jpconstantineau/ErgoTravel/AcrylicCase/Grogdor/pics/2018-05-31 19.27.58.jpg

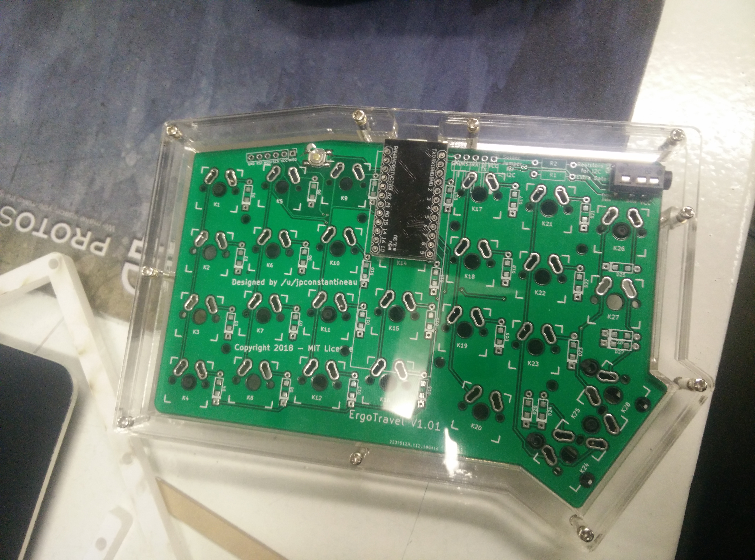
AcrylicCase/Grogdor/pics/2018-05-31 19.27.58.jpg
