jpconstantineau/ErgoTravel/AcrylicCase/Grogdor/pics/2018-05-31 19.28.22.jpg

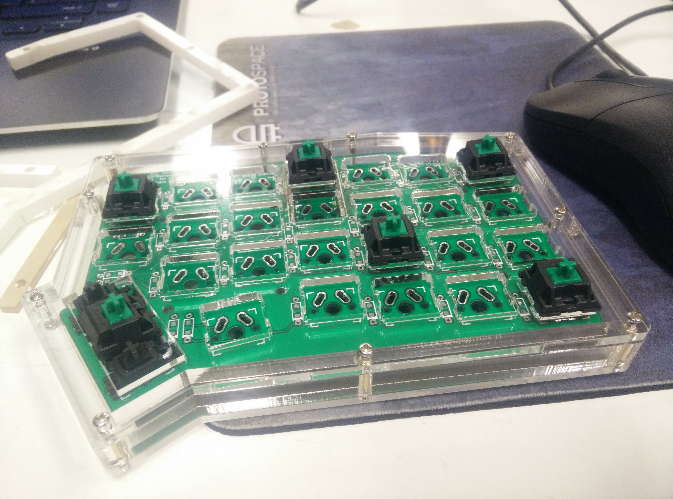
AcrylicCase/Grogdor/pics/2018-05-31 19.28.22.jpg
