jpconstantineau/ErgoTravel/AcrylicCase/Grogdor/pics/2018-05-31 21.10.18.jpg

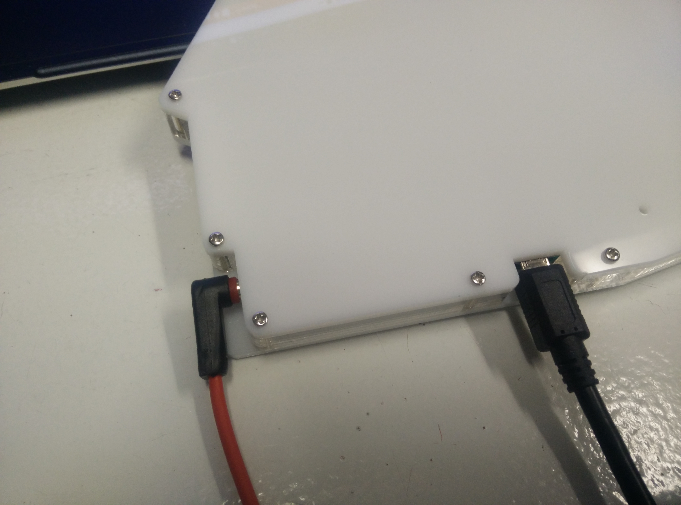
AcrylicCase/Grogdor/pics/2018-05-31 21.10.18.jpg
