jpconstantineau/ErgoTravel/AcrylicCase/Grogdor/pics/2018-05-31 21.10.50.jpg

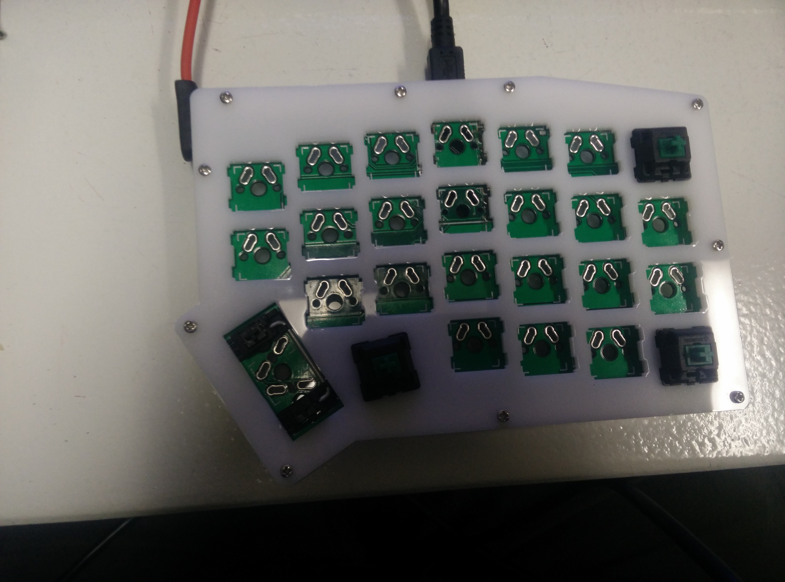
AcrylicCase/Grogdor/pics/2018-05-31 21.10.50.jpg
