jpconstantineau/ErgoTravel/AcrylicCase/Grogdor/pics/2018-05-31 21.47.54.jpg

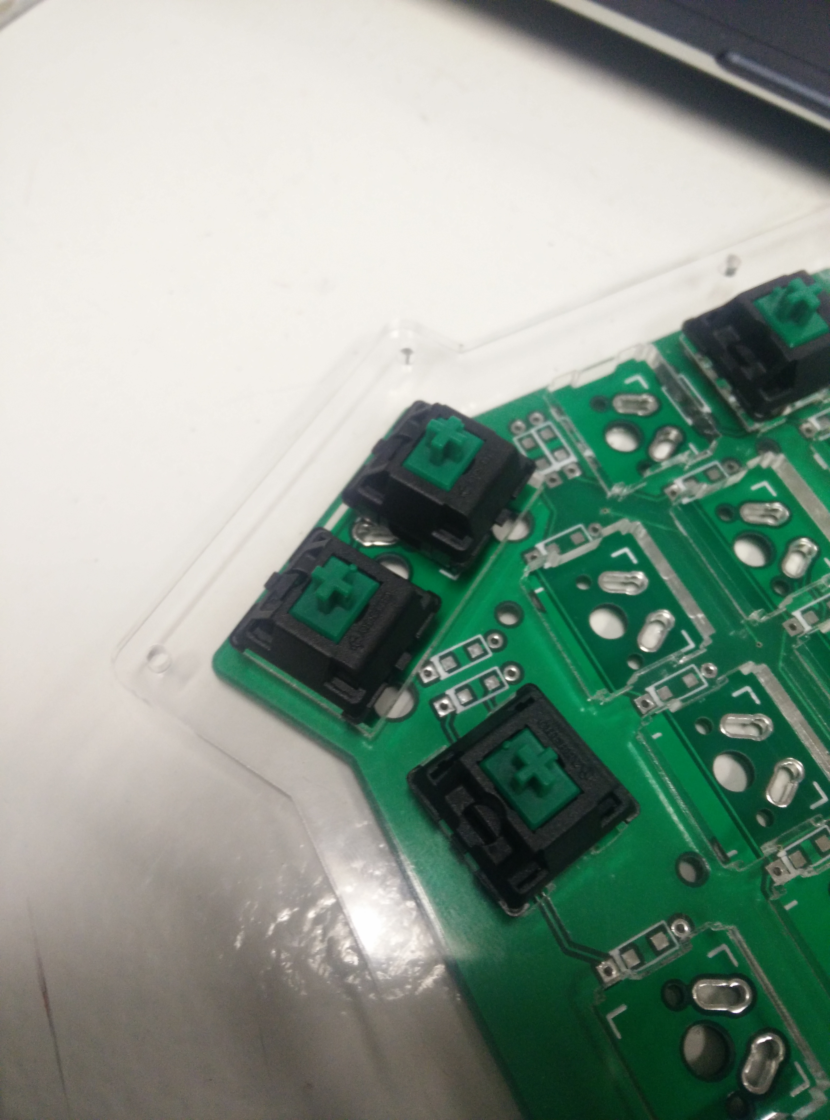
AcrylicCase/Grogdor/pics/2018-05-31 21.47.54.jpg
