jpconstantineau/ErgoTravel/AcrylicCase/Grogdor/pics/2018-05-31 21.59.58.jpg

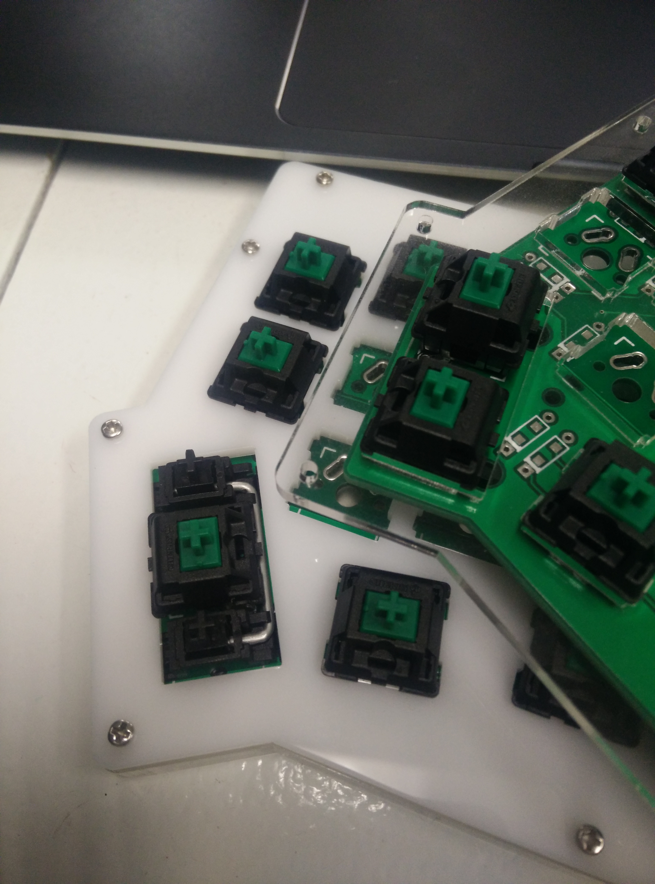
AcrylicCase/Grogdor/pics/2018-05-31 21.59.58.jpg
