jpconstantineau/ErgoTravel/AcrylicCase/Grogdor/pics/2018-05-31 22.29.56.jpg

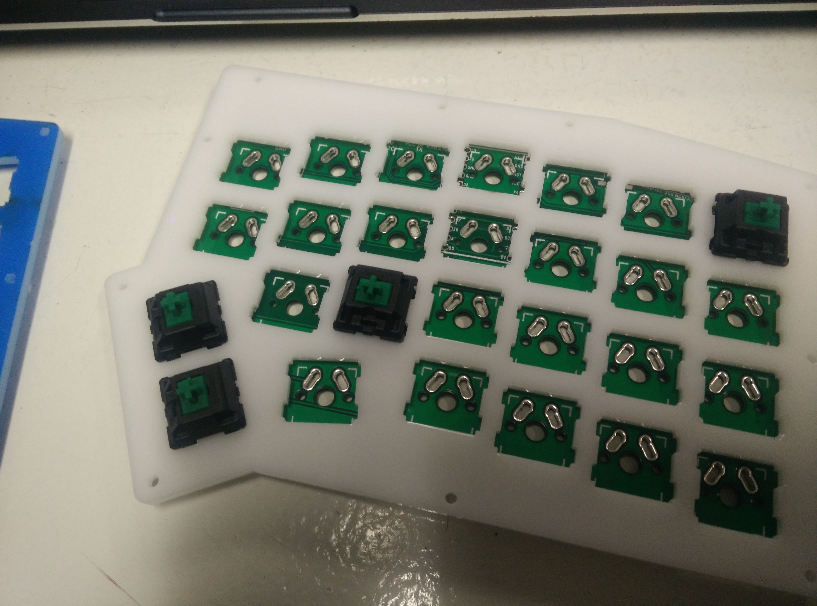
AcrylicCase/Grogdor/pics/2018-05-31 22.29.56.jpg
