jpconstantineau/ErgoTravel/AcrylicCase/Grogdor/pics/2018-06-26 22.19.27c.jpg

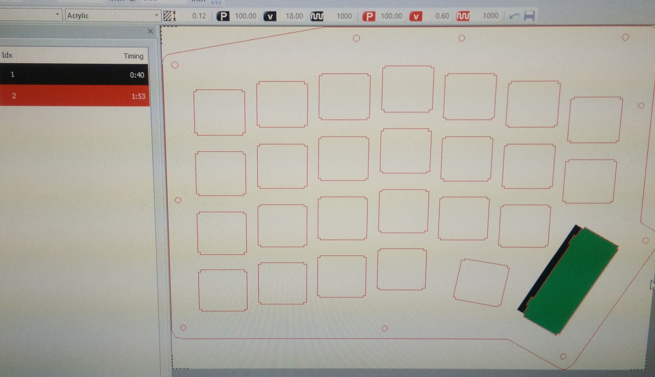
AcrylicCase/Grogdor/pics/2018-06-26 22.19.27c.jpg
