jpconstantineau/ErgoTravel/AcrylicCase/Grogdor/pics/2018-06-26 22.31.41.jpg

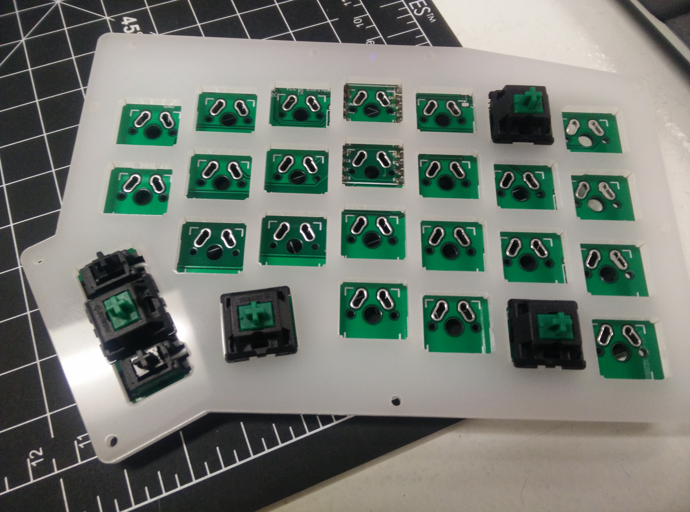
AcrylicCase/Grogdor/pics/2018-06-26 22.31.41.jpg
