jpconstantineau/ErgoTravel/AcrylicCase/Grogdor/pics/2018-06-26 22.33.23.jpg

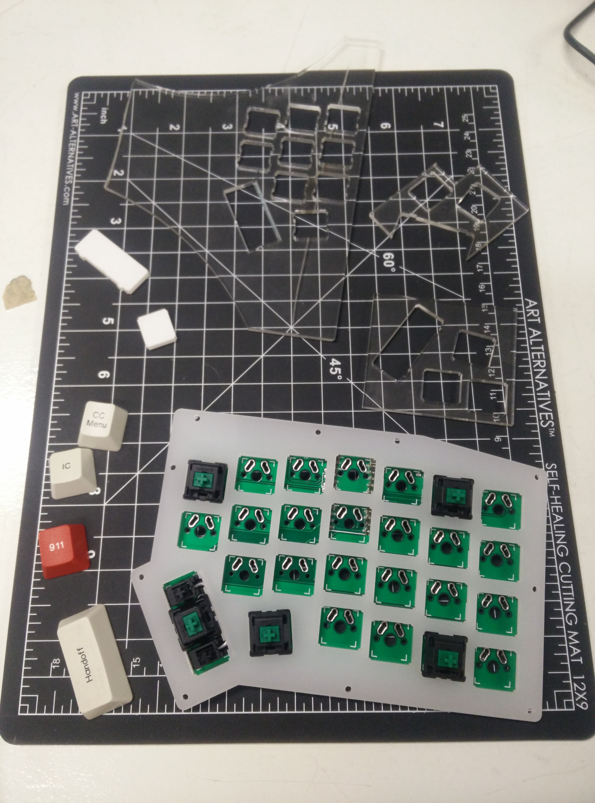
AcrylicCase/Grogdor/pics/2018-06-26 22.33.23.jpg
