jpconstantineau/ErgoTravel/AcrylicCase/Grogdor/pics/2018-06-26 22.34.32.jpg

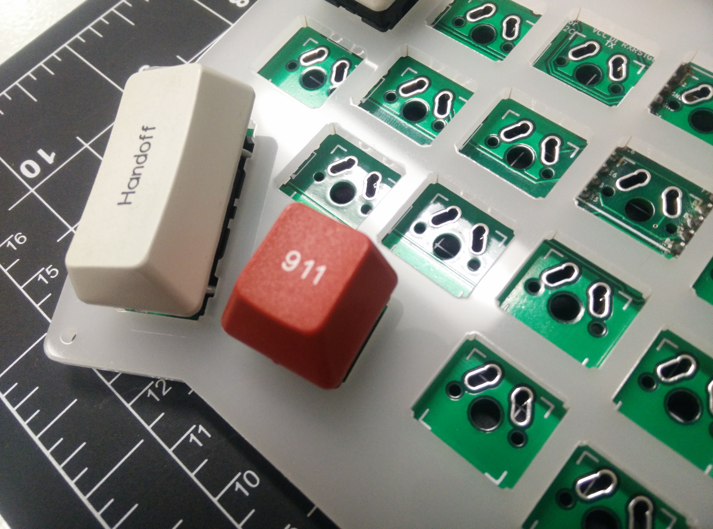
AcrylicCase/Grogdor/pics/2018-06-26 22.34.32.jpg
