jpconstantineau/ErgoTravel/AcrylicCase/Grogdor/pics/2018-06-26 22.34.40c.jpg

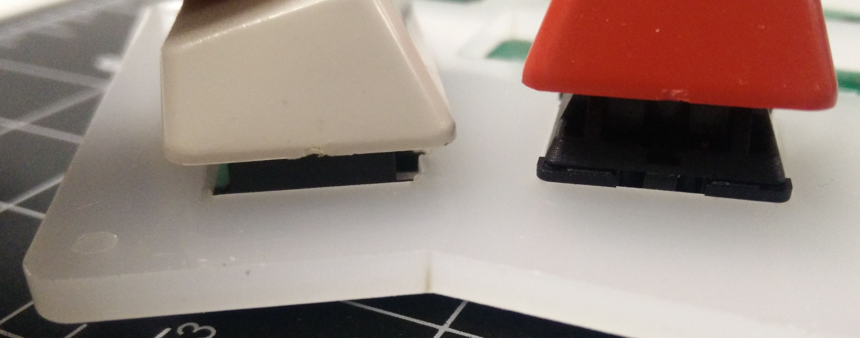
AcrylicCase/Grogdor/pics/2018-06-26 22.34.40c.jpg
