jpconstantineau/ErgoTravel/AcrylicCase/Grogdor/pics/2018-06-26 22.37.25.jpg

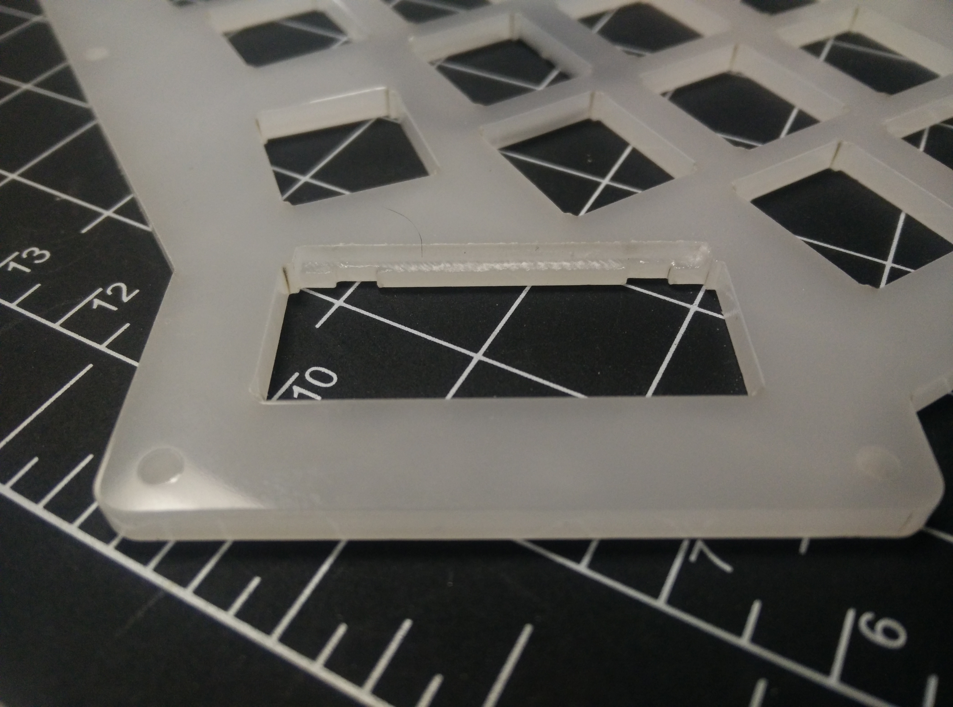
AcrylicCase/Grogdor/pics/2018-06-26 22.37.25.jpg
