jpconstantineau/ErgoTravel/ExternalPCBCase/BottomPlate/Bottom Plate.png

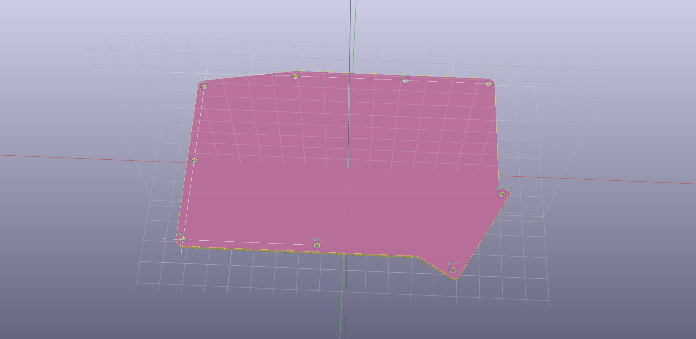
ExternalPCBCase/BottomPlate/Bottom Plate.png
