jpconstantineau/ErgoTravel/ExternalPCBCase/TopPlate1U/Top Plate.png

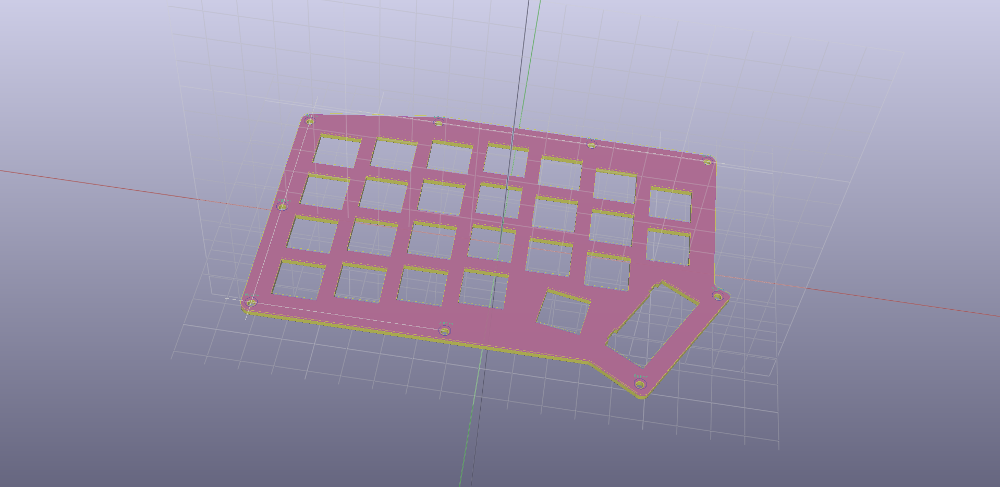
ExternalPCBCase/TopPlate1U/Top Plate.png
