jpconstantineau/ErgoTravel/images/Case_PCB.PNG

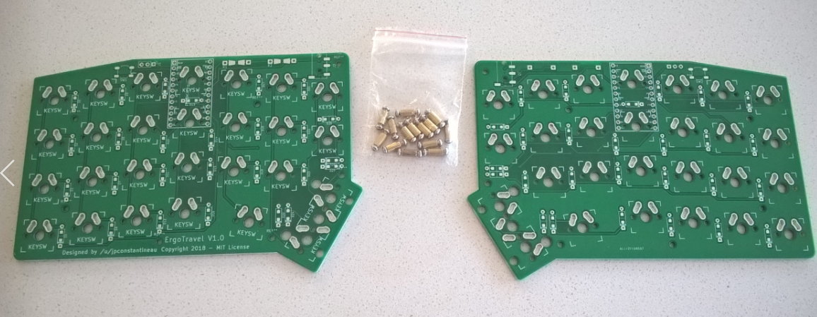
images/Case_PCB.PNG
