jpconstantineau/ErgoTravel/images/Case_Sandwich.PNG

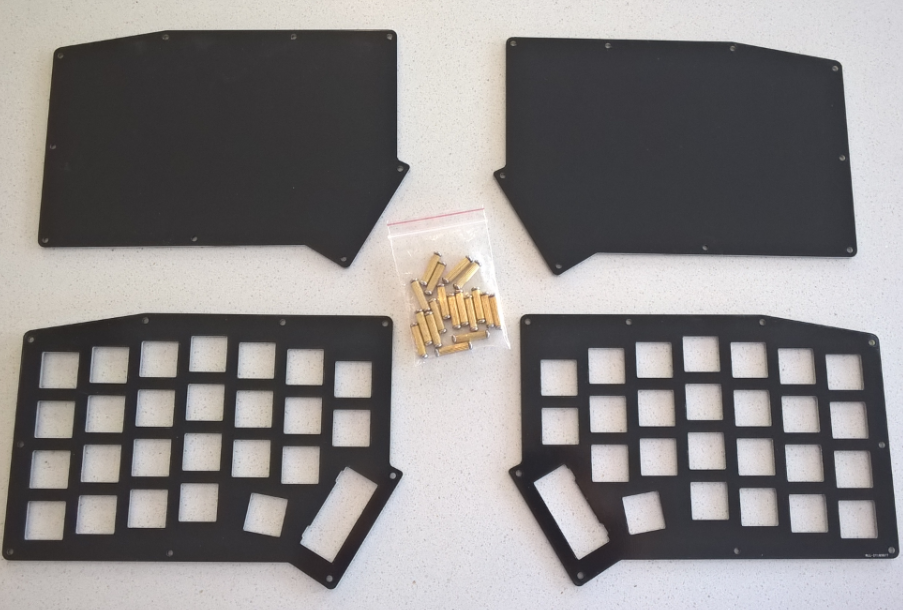
images/Case_Sandwich.PNG
