jpconstantineau/ErgoTravel/images/diodes_back.png

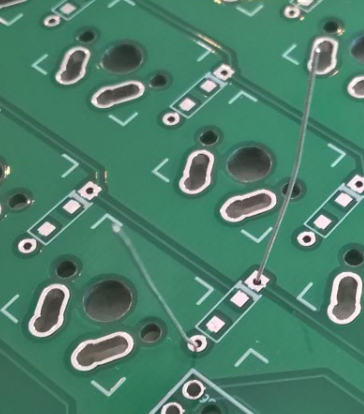
images/diodes_back.png
