jpconstantineau/ErgoTravel/images/first_alps_ergotravel_top.jpg

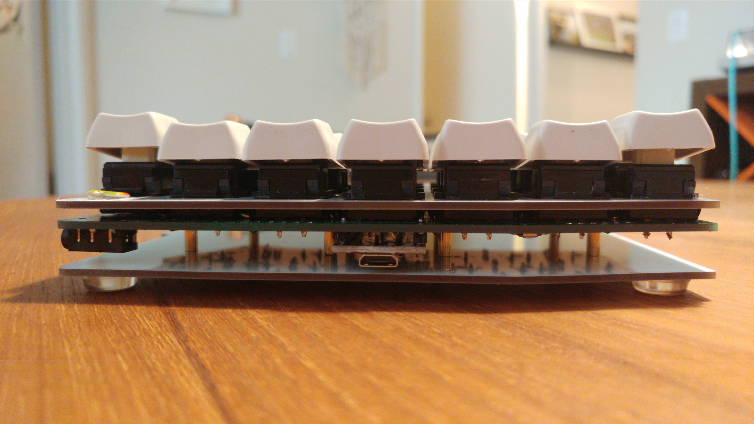
images/first_alps_ergotravel_top.jpg
