jpconstantineau/ErgoTravel/images/Full_Kit.PNG

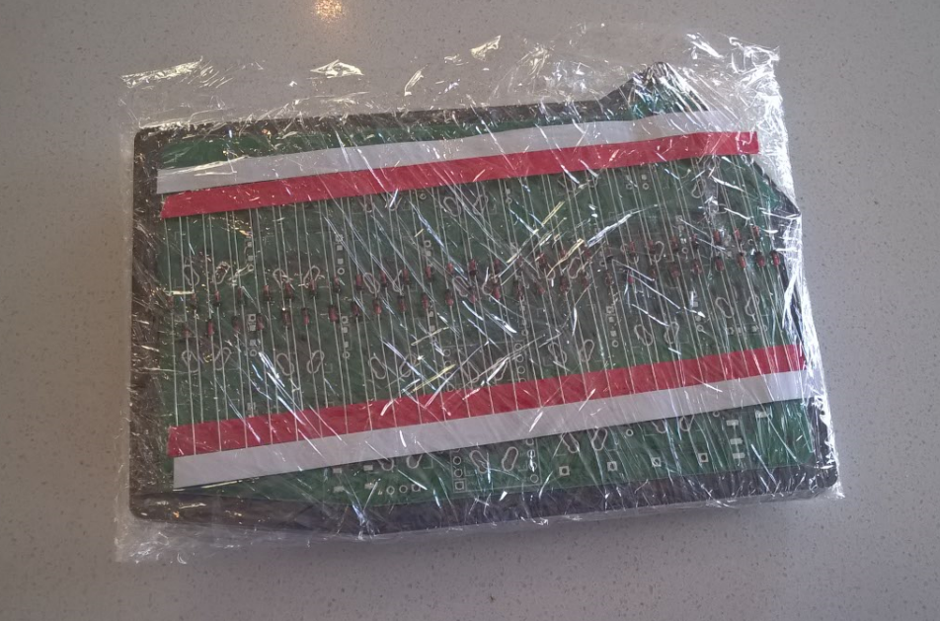
images/Full_Kit.PNG
