jpconstantineau/ErgoTravel/images/Key_Matrix.PNG

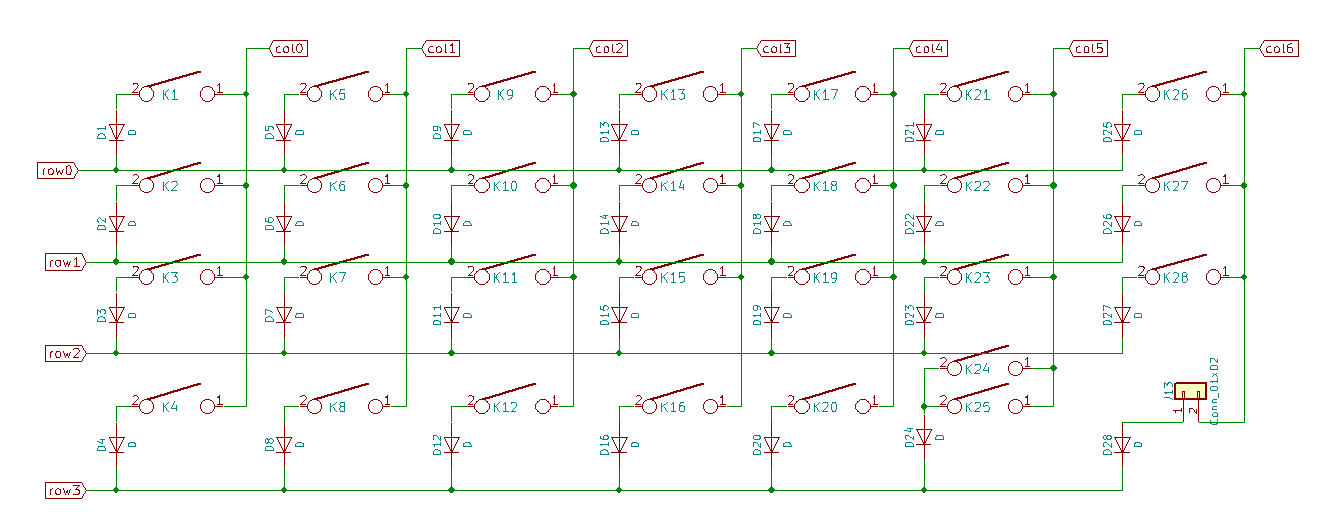
images/Key_Matrix.PNG
