jpconstantineau/ErgoTravel/images/keyboard-layout.2x1U_1x2U.png

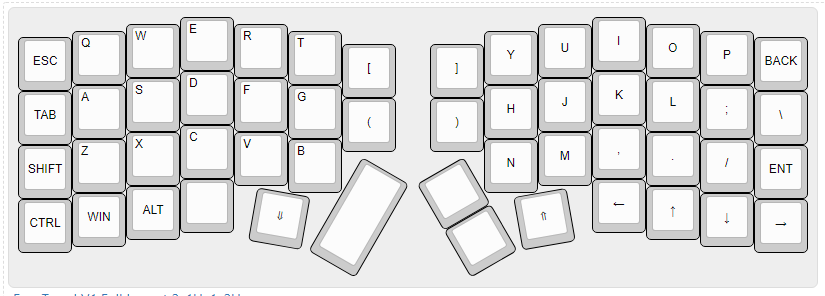
images/keyboard-layout.2x1U_1x2U.png
