jpconstantineau/ErgoTravel/images/PCB_V1.0_Left.PNG

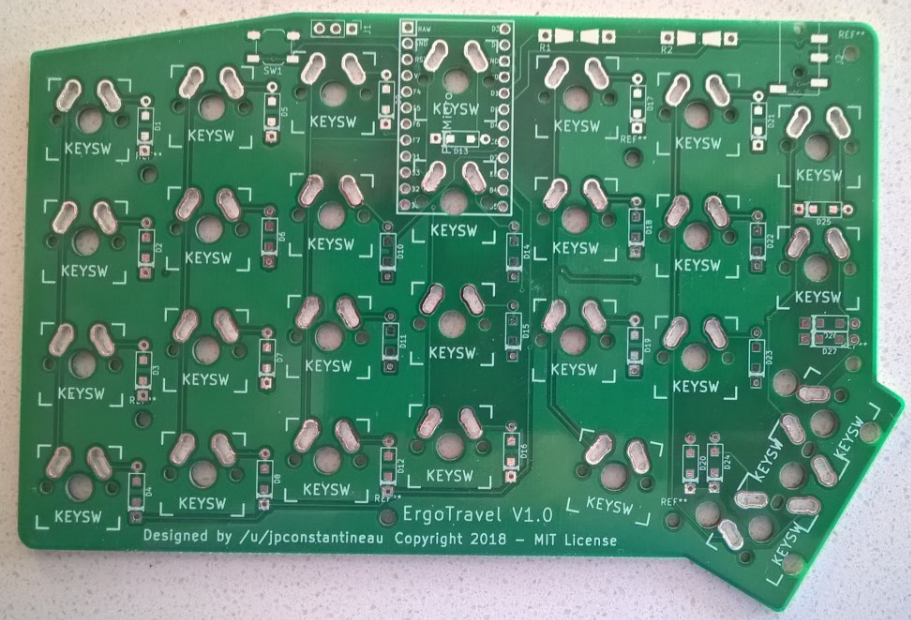
images/PCB_V1.0_Left.PNG
