jpconstantineau/ErgoTravel/images/PCB_V1.0_Right.PNG

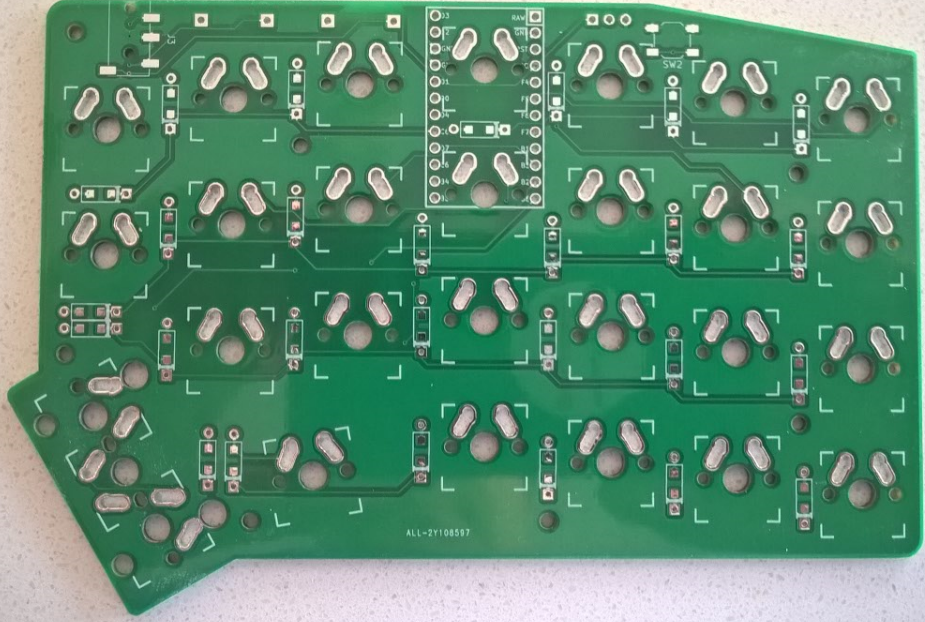
images/PCB_V1.0_Right.PNG
