jpconstantineau/ErgoTravel/images/RGB_strip_connections.jpg

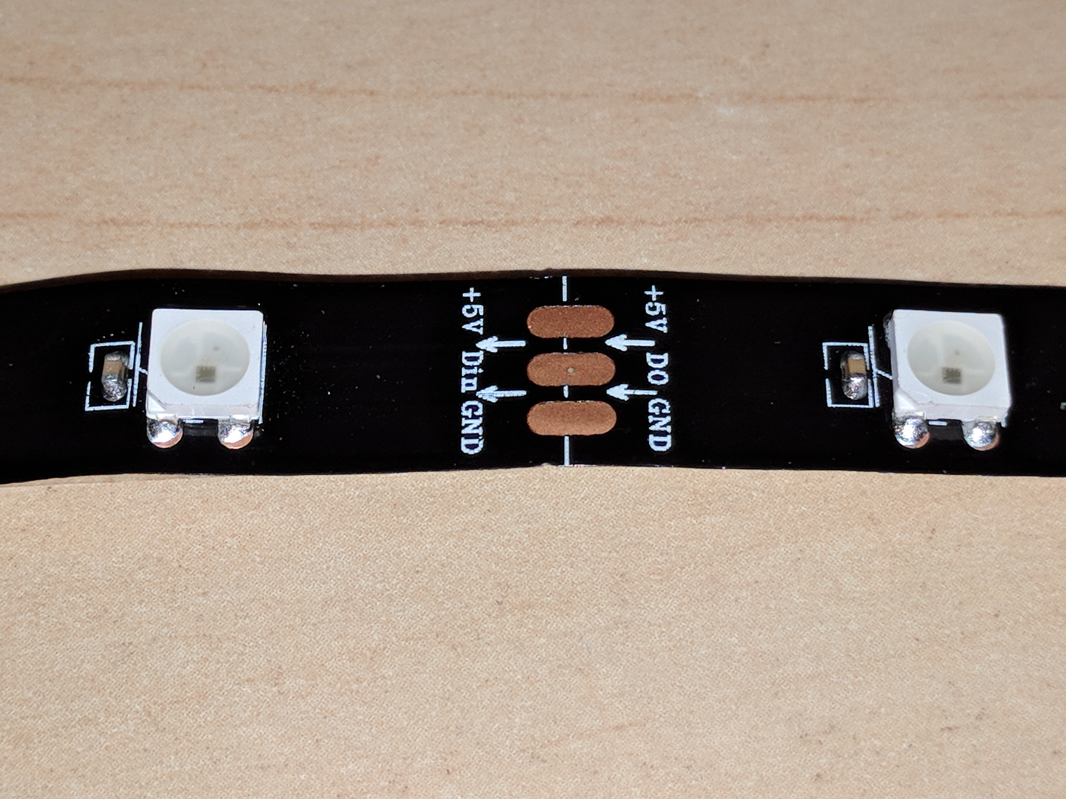
images/RGB_strip_connections.jpg
