jpconstantineau/ErgoTravel/images/stabilizerlegs_1.png

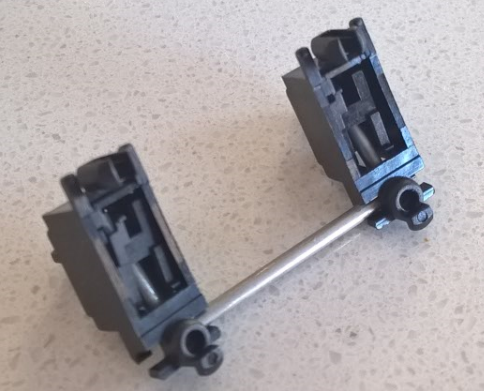
images/stabilizerlegs_1.png
