jpconstantineau/ErgoTravel/PCB/ErgoTravelPCBV1.PNG

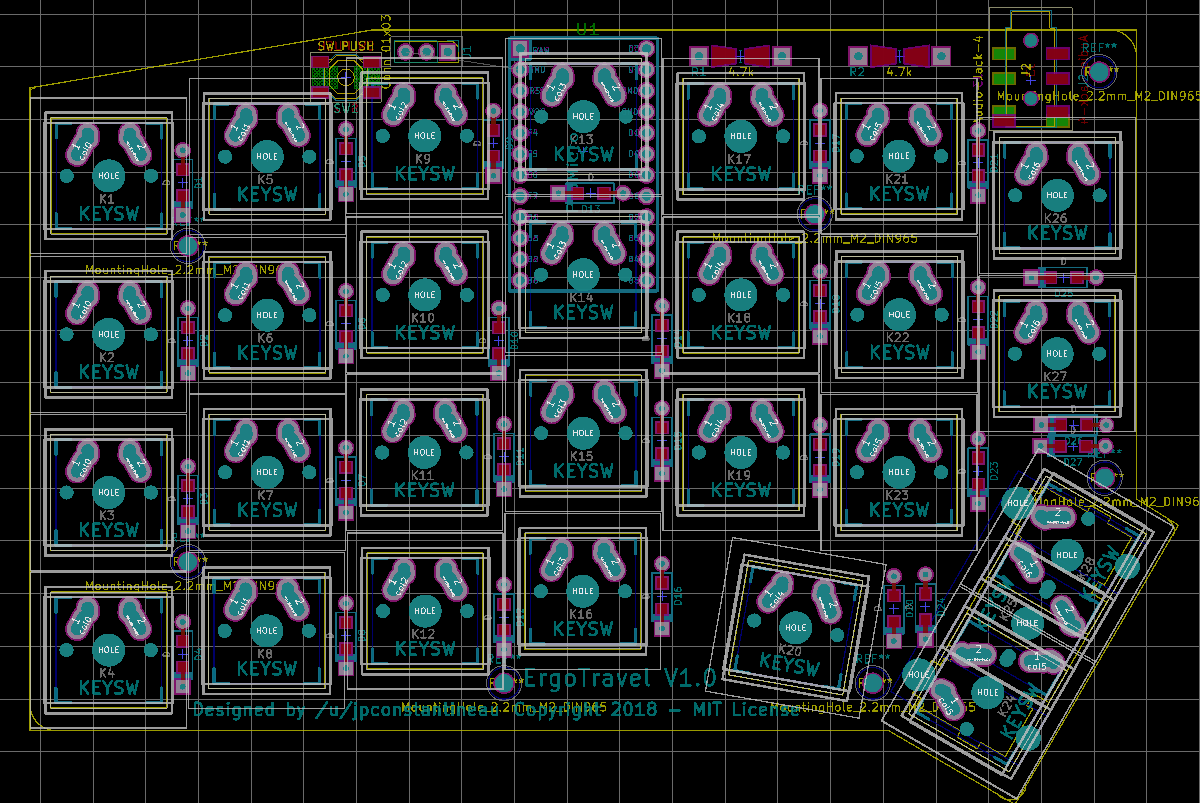
PCB/ErgoTravelPCBV1.PNG
