jpconstantineau/ErgoTravel/Reference/Kailh-.png

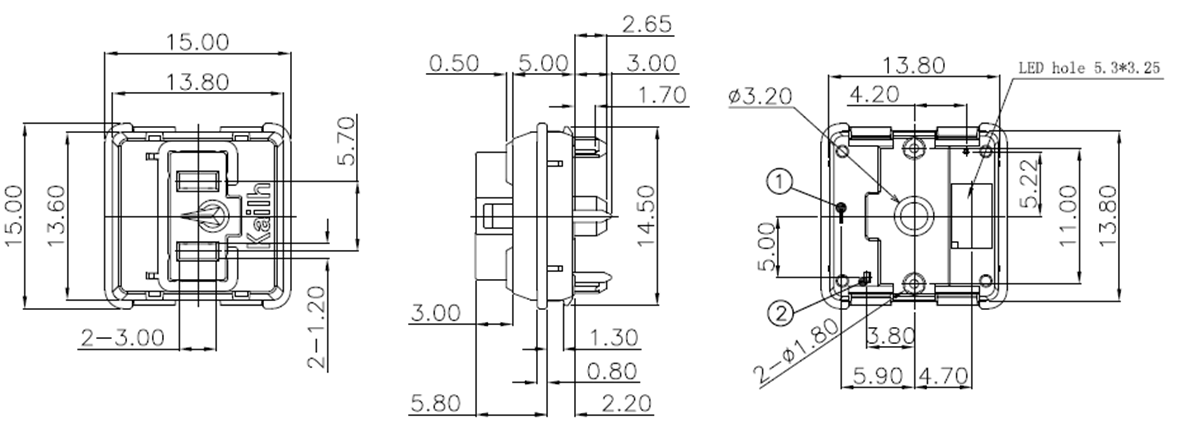
Reference/Kailh-.png
