jpconstantineau/ErgoTravel/AcrylicCase/Grogdor/everything DFM8.dxf

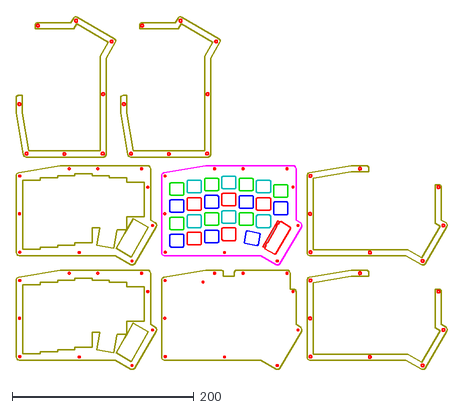
[picture p61: CAD file, 2019-04-07]
AcrylicCase/Grogdor/everything DFM8.dxf
474.9 x 388.8
