jpconstantineau/ErgoTravel/AcrylicCase/jpconstantineau/3dMids/3dmids_prototype_3.stl

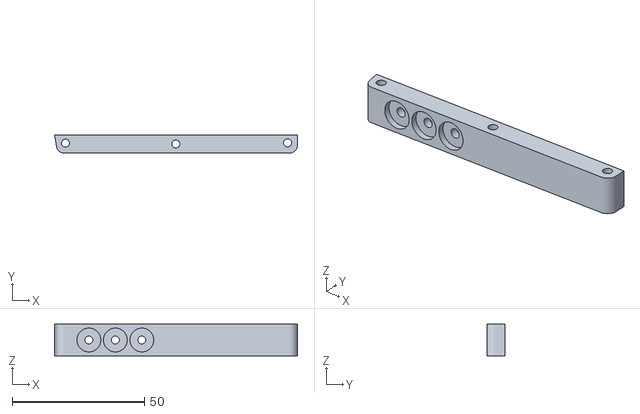
[picture p62: CAD file, 2019-11-17]
AcrylicCase/jpconstantineau/3dMids/3dmids_prototype_3.stl
91.8 x 6.89 x 12.0
