jpconstantineau/ErgoTravel/ExternalPCBCase/BottomPlate/Bottom Plate-F.Cu.dxf

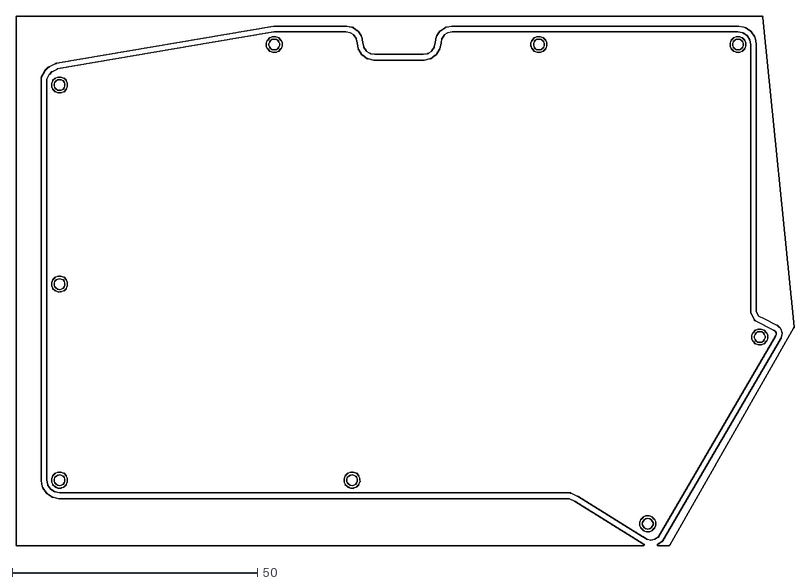
[picture p63: CAD file, 2018-06-02]
ExternalPCBCase/BottomPlate/Bottom Plate-F.Cu.dxf
158.7 x 108.0
