jpconstantineau/ErgoTravel/ExternalPCBCase/TopPlateCombined/Top Plate-brd.dxf

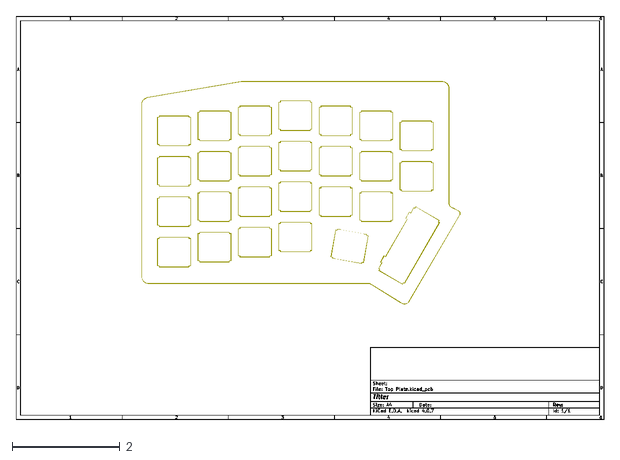
[picture p64: CAD file, 2018-06-02]
ExternalPCBCase/TopPlateCombined/Top Plate-brd.dxf
10.9 x 7.49
