jpconstantineau/ErgoTravel/InternalPCBCase/TopPlate2U/TravelDox-Eco2.User.dxf

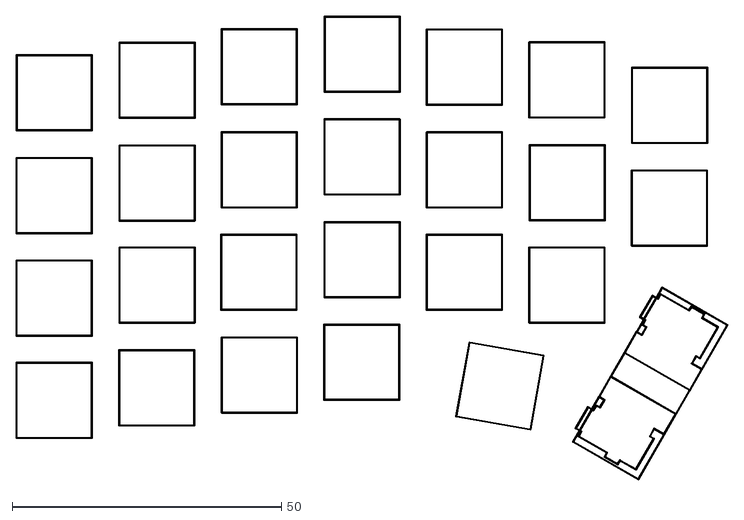
[picture p65: CAD file, 2018-03-09]
InternalPCBCase/TopPlate2U/TravelDox-Eco2.User.dxf
132.2 x 86.1
