jpconstantineau/ErgoTravel/Layout/ErgoTravel_2U_MX.dxf

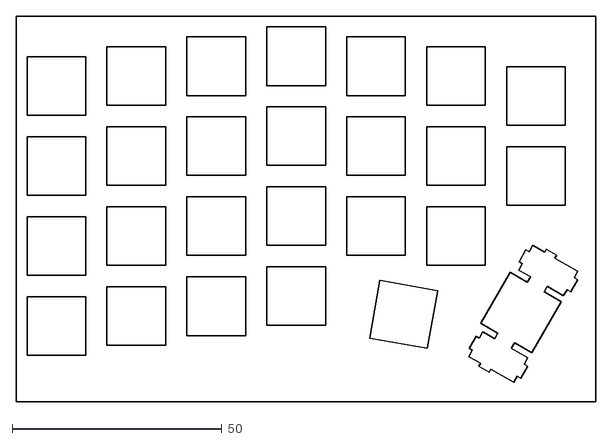
[picture p66: CAD file, 2018-03-09]
Layout/ErgoTravel_2U_MX.dxf
138.0 x 91.9
