jpconstantineau/ErgoTravel/3DPrintedCase/jpconstantineau/MxApls10degree.dxf

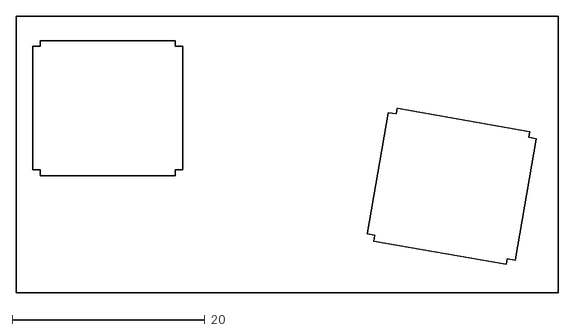
[picture p67: CAD file, 2018-05-28]
3DPrintedCase/jpconstantineau/MxApls10degree.dxf
56.3 x 28.7
