jpconstantineau/ErgoTravel/3DPrintedCase/lbibass/low_profile_right.stl

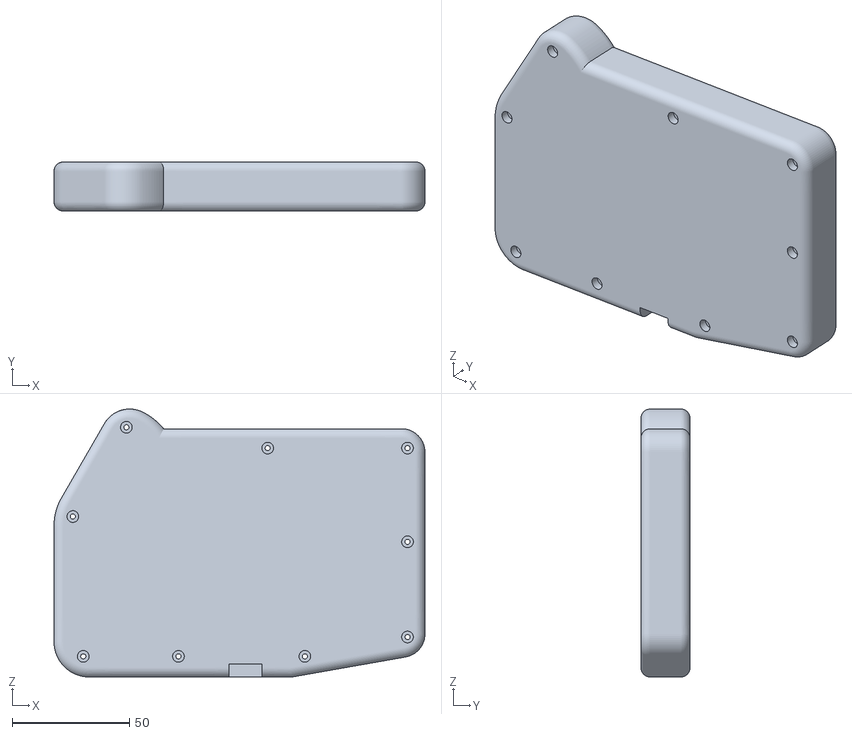
[picture p68: CAD file, 2018-05-11]
3DPrintedCase/lbibass/low_profile_right.stl
158.4 x 21.0 x 114.4
