jpconstantineau/ErgoTravel/AcrylicCase/Grogdor/hipro only bluemicro DFM9.dxf

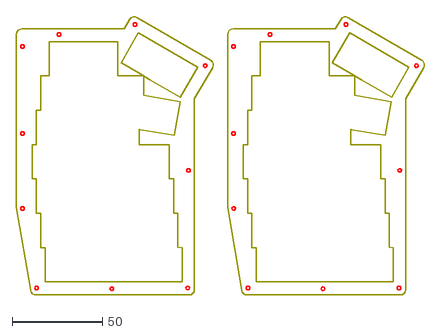
[picture p69: CAD file, 2019-04-07]
AcrylicCase/Grogdor/hipro only bluemicro DFM9.dxf
226.7 x 154.9
