jpconstantineau/ErgoTravel/ExternalPCBCase/BottomPlate/Bottom Plate-B.Cu.dxf

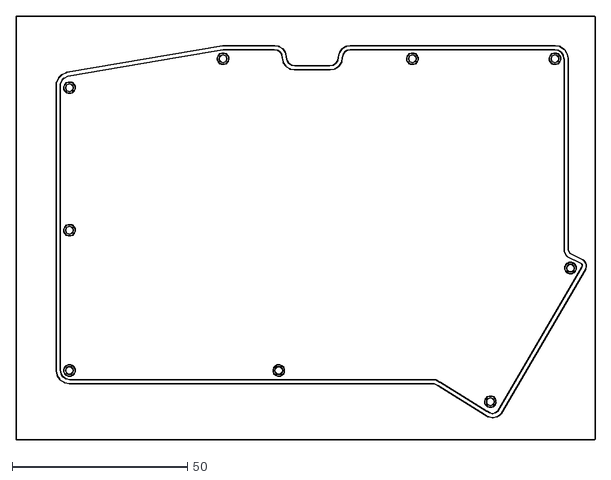
[picture p70: CAD file, 2018-06-02]
ExternalPCBCase/BottomPlate/Bottom Plate-B.Cu.dxf
165.1 x 120.7
