jpconstantineau/ErgoTravel/ExternalPCBCase/TopPlate1U/Top Plate-Edge.Cuts.dxf

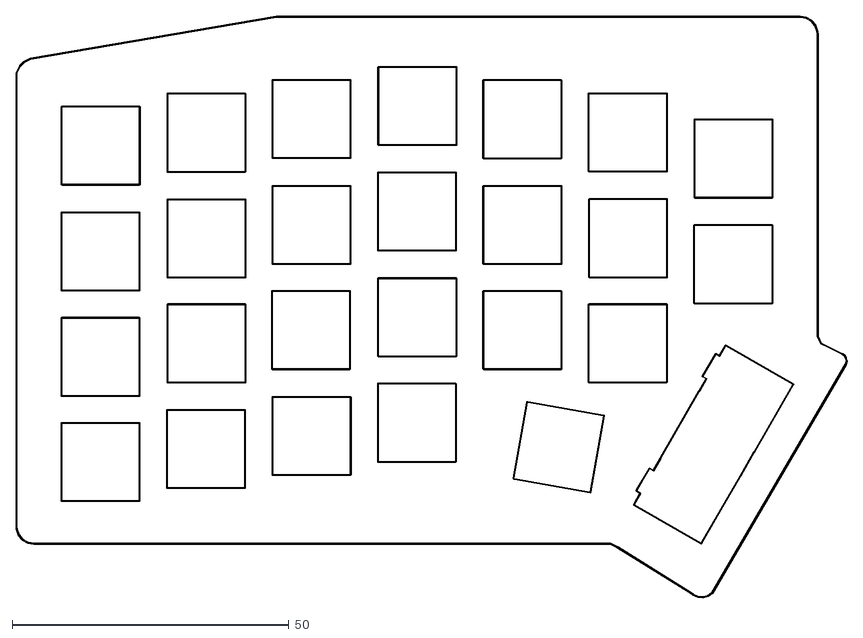
[picture p71: CAD file, 2018-04-29]
ExternalPCBCase/TopPlate1U/Top Plate-Edge.Cuts.dxf
150.2 x 105.1
