jpconstantineau/ErgoTravel/ExternalPCBCase/TopPlateCombined/Top Plate-Edge.Cuts.dxf

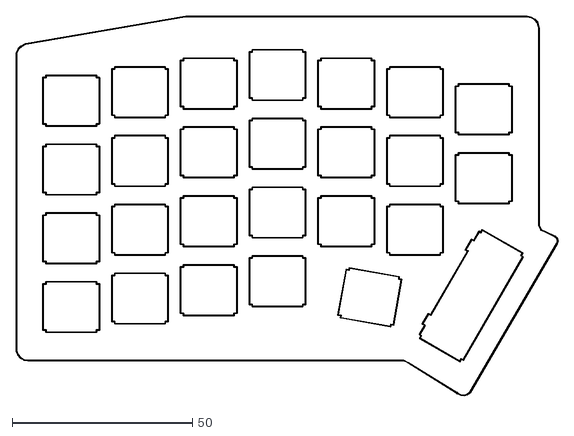
[picture p72: CAD file, 2018-06-02]
ExternalPCBCase/TopPlateCombined/Top Plate-Edge.Cuts.dxf
150.2 x 105.1
