jpconstantineau/ErgoTravel/Layout/ErgoTravel_1u.dxf

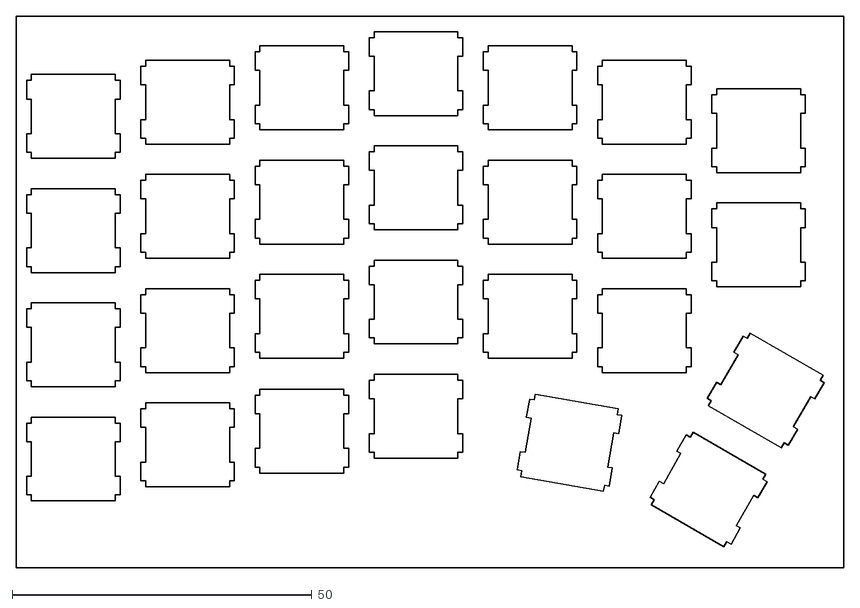
[picture p73: CAD file, 2018-03-09]
Layout/ErgoTravel_1u.dxf
138.0 x 91.9
