jpconstantineau/ErgoTravel/3DPrintedCase/jpconstantineau/MXAlps.dxf

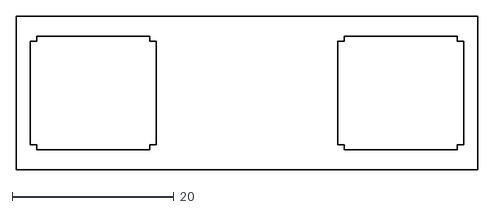
[picture p74: CAD file, 2018-05-28]
3DPrintedCase/jpconstantineau/MXAlps.dxf
57.2 x 19.0
