jpconstantineau/ErgoTravel/AcrylicCase/Grogdor/top only bluemicro DFM9.dxf

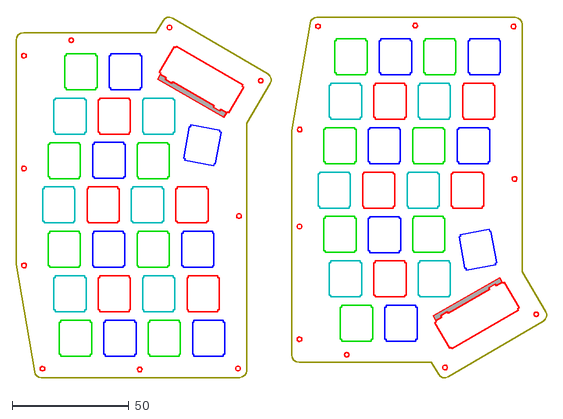
[picture p75: CAD file, 2019-04-07]
AcrylicCase/Grogdor/top only bluemicro DFM9.dxf
227.6 x 155.4
