jpconstantineau/ErgoTravel/AcrylicCase/jpconstantineau/3dMids/3dmids_prototype.stl

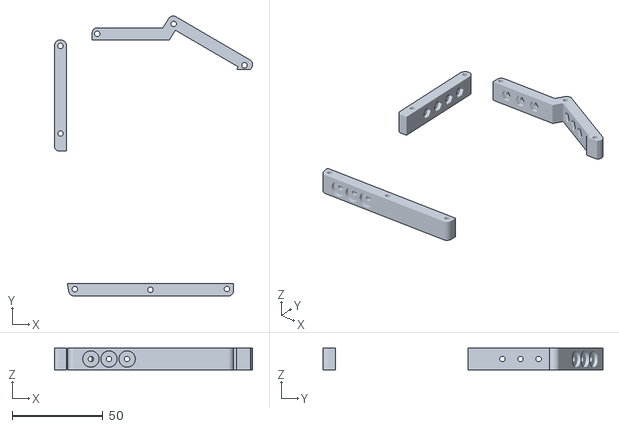
[picture p76: CAD file, 2019-11-17]
AcrylicCase/jpconstantineau/3dMids/3dmids_prototype.stl
109.3 x 154.5 x 12.0
