jpconstantineau/ErgoTravel/Layout/ErgoTravel_1U_MX.dxf

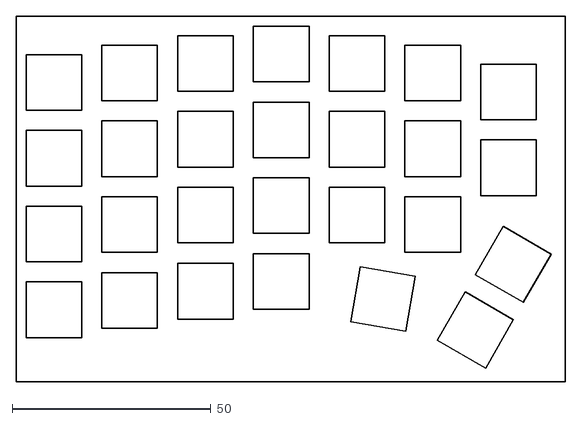
[picture p77: CAD file, 2018-03-09]
Layout/ErgoTravel_1U_MX.dxf
138.0 x 91.9
