jpconstantineau/ErgoTravel/3DPrintedCase/jpconstantineau/mxalps2u30degree.dxf

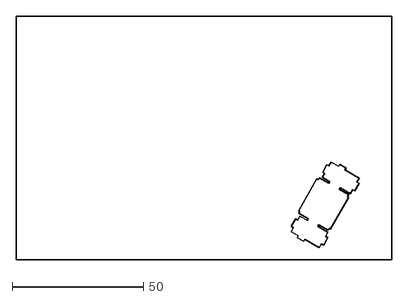
[picture p78: CAD file, 2018-05-28]
3DPrintedCase/jpconstantineau/mxalps2u30degree.dxf
142.9 x 92.8
