jpconstantineau/ErgoTravel/AcrylicCase/Grogdor/bottoms only DFM8.dxf

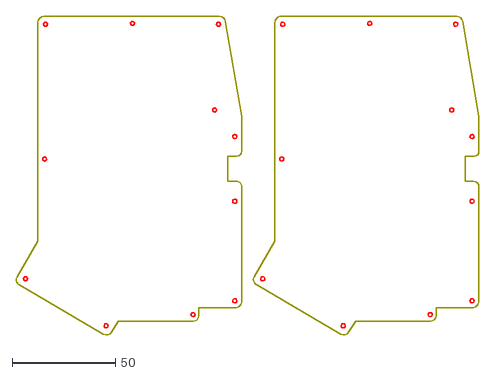
[picture p79: CAD file, 2019-04-07]
AcrylicCase/Grogdor/bottoms only DFM8.dxf
224.4 x 154.9
