jpconstantineau/ErgoTravel/AcrylicCase/jpconstantineau/3dMids/mids only DFM8.dxf

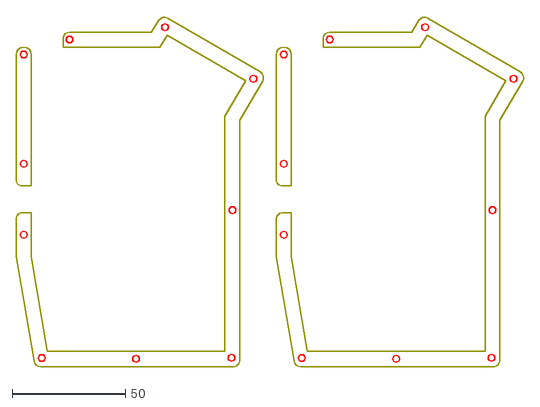
[picture p80: CAD file, 2019-04-07]
AcrylicCase/jpconstantineau/3dMids/mids only DFM8.dxf
224.4 x 154.9
