jpconstantineau/ErgoTravel/3DPrintedCase/jpconstantineau/mxapls30degree.dxf

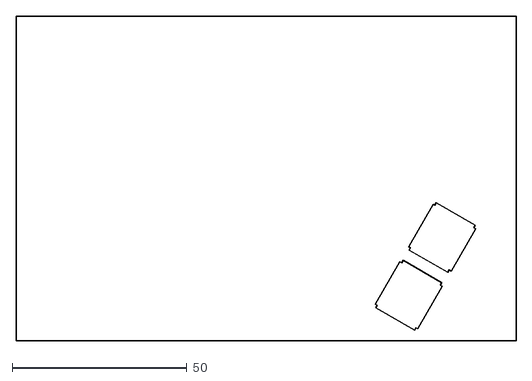
[picture p81: CAD file, 2018-05-28]
3DPrintedCase/jpconstantineau/mxapls30degree.dxf
142.9 x 92.8
