jpconstantineau/ErgoTravel/AcrylicCase/Grogdor/bottoms only bluemicro DFM9.dxf

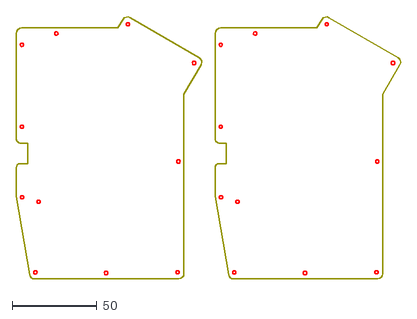
[picture p82: CAD file, 2019-04-07]
AcrylicCase/Grogdor/bottoms only bluemicro DFM9.dxf
226.7 x 154.9
