jpconstantineau/ErgoTravel/3DPrintedCase/jpconstantineau/2UMX.dxf

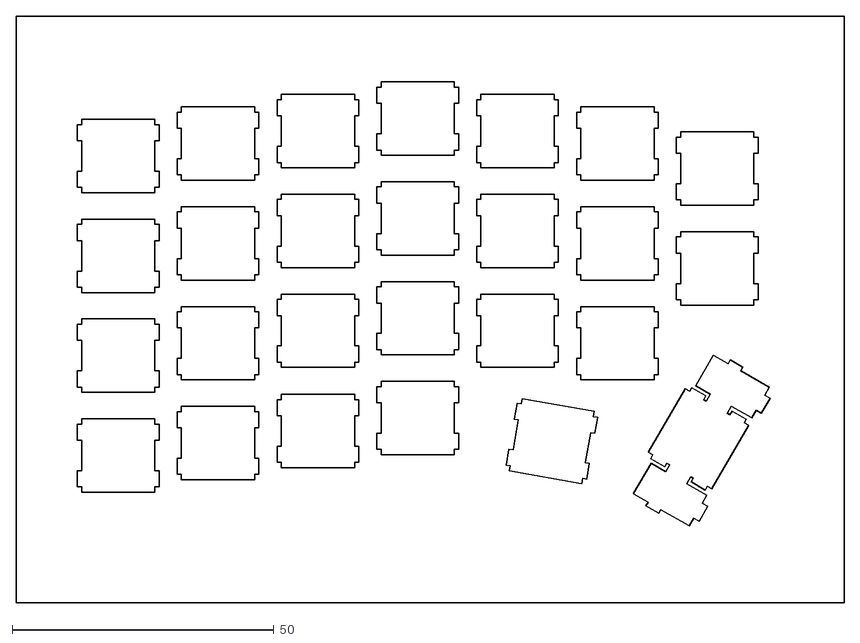
[picture p83: CAD file, 2018-03-27]
3DPrintedCase/jpconstantineau/2UMX.dxf
158.0 x 111.9
