jpconstantineau/ErgoTravel/3DPrintedCase/jpconstantineau/1UMXApls.dxf

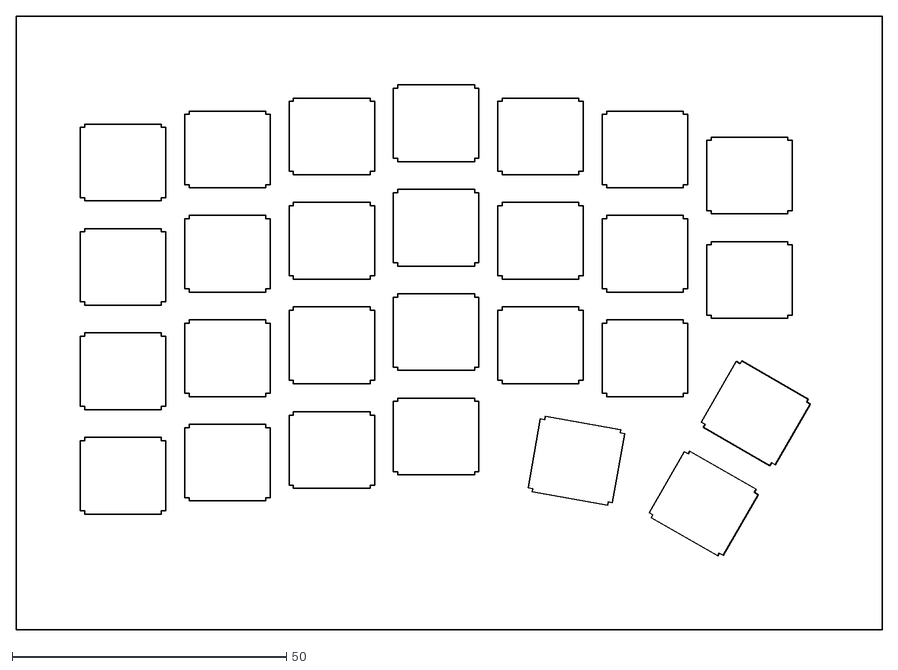
[picture p84: CAD file, 2018-03-27]
3DPrintedCase/jpconstantineau/1UMXApls.dxf
158.0 x 111.9
