jpconstantineau/ErgoTravel/AcrylicCase/Grogdor/midlittles only DFM8.dxf

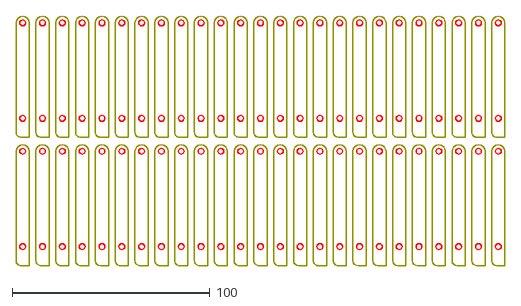
[picture p85: CAD file, 2019-04-07]
AcrylicCase/Grogdor/midlittles only DFM8.dxf
247.5 x 126.3
