jpconstantineau/ErgoTravel/3DPrintedCase/jpconstantineau/1UMX.dxf

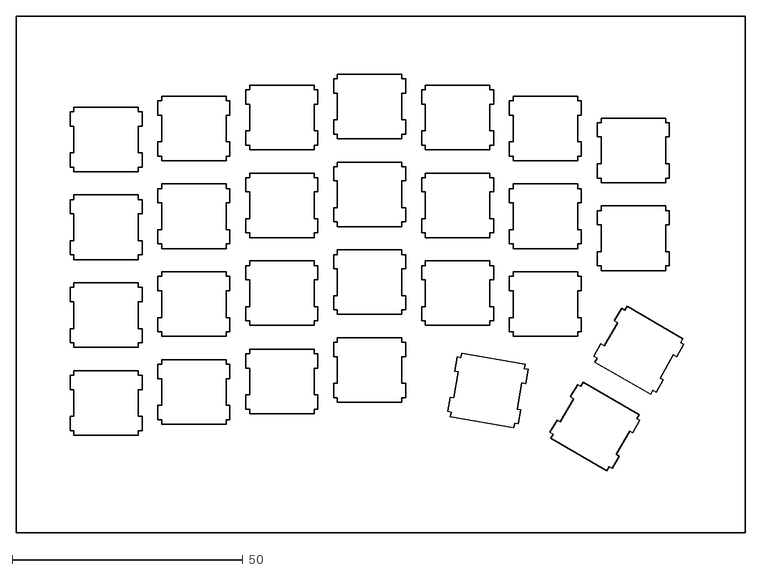
[picture p86: CAD file, 2018-03-27]
3DPrintedCase/jpconstantineau/1UMX.dxf
158.0 x 111.9
