jpconstantineau/ErgoTravel/AcrylicCase/Grogdor/everything nite.dxf

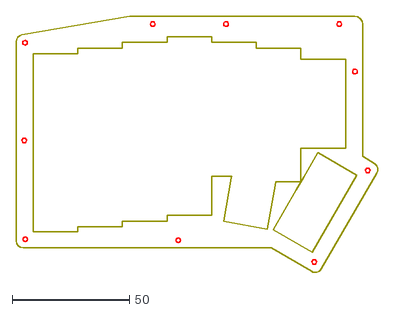
[picture p87: CAD file, 2019-04-07]
AcrylicCase/Grogdor/everything nite.dxf
154.9 x 109.4
