jpconstantineau/ErgoTravel/3DPrintedCase/jpconstantineau/MXAlps2.dxf

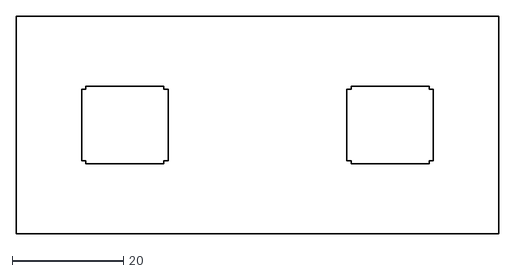
[picture p88: CAD file, 2018-03-27]
3DPrintedCase/jpconstantineau/MXAlps2.dxf
86.7 x 39.1
