jpconstantineau/ErgoTravel/AcrylicCase/Grogdor/everything DFM9.dxf

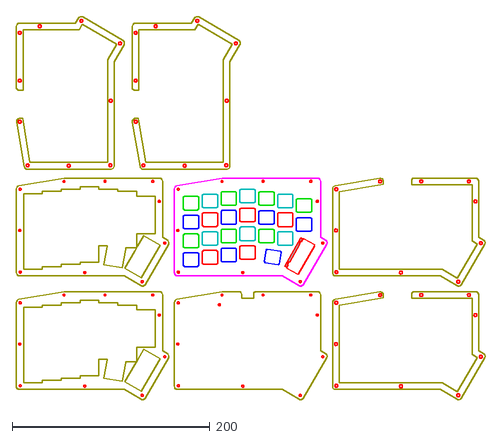
[picture p89: CAD file, 2019-04-07]
AcrylicCase/Grogdor/everything DFM9.dxf
474.9 x 388.3
