jpconstantineau/ErgoTravel/3DPrintedCase/jpconstantineau/MX2.dxf

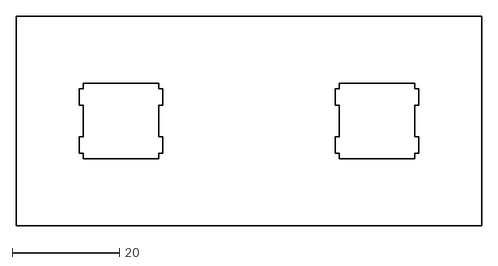
[picture p90: CAD file, 2018-03-27]
3DPrintedCase/jpconstantineau/MX2.dxf
86.7 x 39.1
