jpconstantineau/ErgoTravel/AcrylicCase/Grogdor/hipro only DFM8.dxf

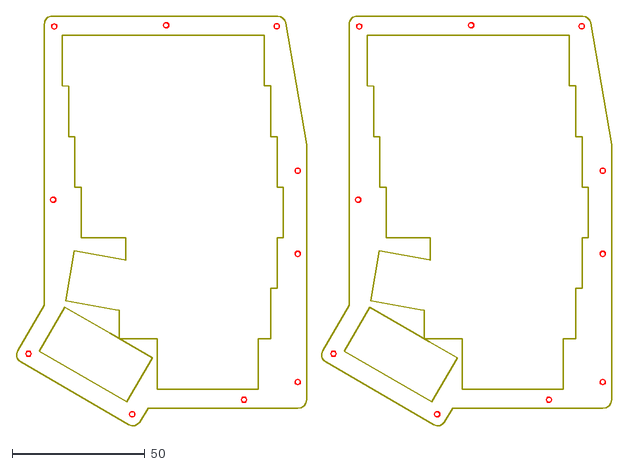
[picture p91: CAD file, 2019-04-07]
AcrylicCase/Grogdor/hipro only DFM8.dxf
224.4 x 154.9
