jpconstantineau/ErgoTravel/3DPrintedCase/jpconstantineau/2UMXAlps.dxf

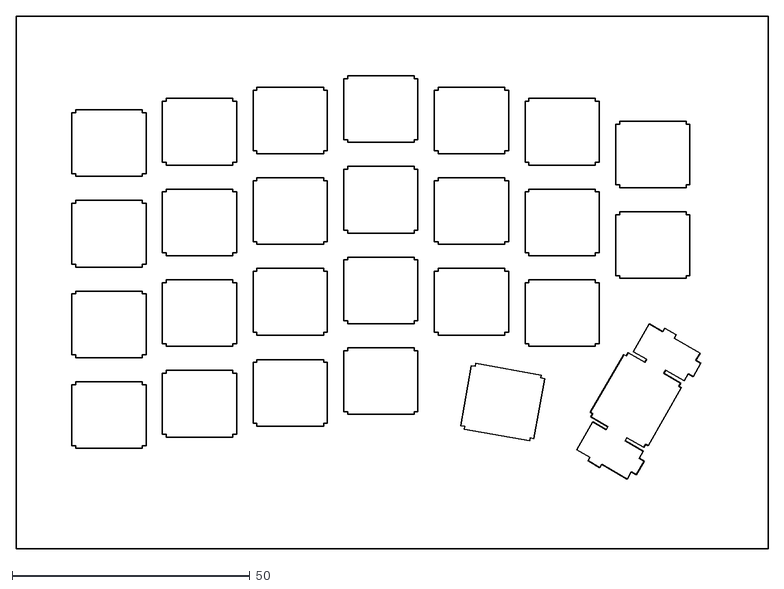
[picture p92: CAD file, 2018-03-27]
3DPrintedCase/jpconstantineau/2UMXAlps.dxf
158.0 x 111.9
