jpconstantineau/ErgoTravel/images/Stab_Assembly_2.PNG

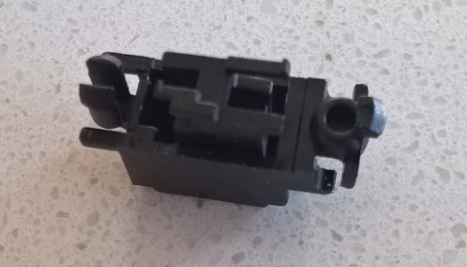
images/Stab_Assembly_2.PNG
